eez-open/dib-mio-afe1/Images/EEZ_DIB_AFE1_PCB_parts.png

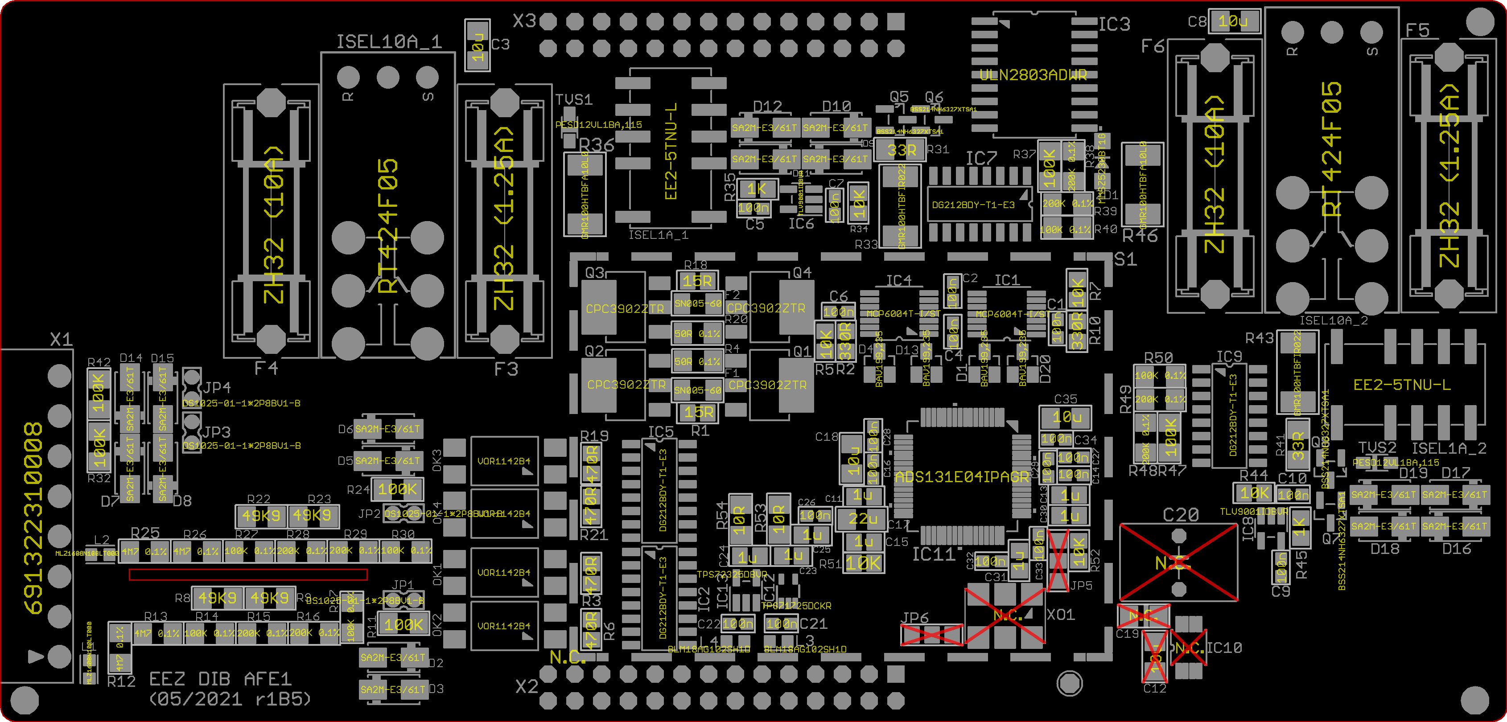
Images/EEZ_DIB_AFE1_PCB_parts.png
